bitfixer/petdisk-max/idf/main/EspHttp.h

#ifndef __esp_http_h__
#define __esp_http_h__

#include "EspConn.h"
#include <stdint.h>

namespace bitfixer
{

struct __attribute__ ((packed)) urlInfo {
    char host[64];
    char url[64];
    char params[64];
    char urlstring[256];
    char blockData[512];
    char fileName[64];
};

class EspHttp 
{
public:
    EspHttp()
    : _espConn(NULL)
    {}

    EspHttp(EspConn* espConn) 
    : _espConn(espConn)
    {}

    ~EspHttp() {}

    void initWithParams(EspConn* espConn);
    bool postBlock(char* host, int port, char* url, char* params, uint8_t* buffer, uint16_t* bufferSize, int numBytes);
    uint8_t* makeRequest(const char* host, int port, const char* url, const char* params, uint8_t* buffer, uint16_t* bufferSize, int* size);
    uint32_t getSize(const char* host, int port, const char* url, uint8_t* buffer, uint16_t* bufferSize);
    uint8_t* getRange(const char* host, int port, const char* url, uint32_t start, uint32_t end, uint8_t* buffer, uint16_t* bufferSize, int* size);

    int getSizeE(const char* host, const char* url, uint8_t* buffer, uint16_t* bufferSize);

private:
    EspConn* _espConn;

    uint8_t sendBuffer[2048];
};

}

#endif
