bitfixer/petdisk-max/idf/main/base64.cpp

/*
* Base64 encoding/decoding (RFC1341)
* Copyright (c) 2005-2011, Jouni Malinen <j@w1.fi>
*
* This software may be distributed under the terms of the BSD license.
* See README for more details.
*/
#include "base64.hpp"
#include <string.h>

static const unsigned char base64_table[65] =
    "ABCDEFGHIJKLMNOPQRSTUVWXYZabcdefghijklmnopqrstuvwxyz0123456789+/";

/**
* base64_encode - Base64 encode
* @src: Data to be encoded
* @len: Length of the data to be encoded
* @out_len: Pointer to output length variable, or %NULL if not used
* Returns: Allocated buffer of out_len bytes of encoded data,
* or empty string on failure
*/
int base64_len(int len) {
    return 4*((len + 2) / 3);
}

int base64_encode(const uint8_t* src, int len, uint8_t* out)
{
    unsigned char *pos;
    const unsigned char *end, *in;

    int olen = base64_len(len);

    end = src + len;
    in = src;
    pos = out;
    while (end - in >= 3) {
        *pos++ = base64_table[in[0] >> 2];
        *pos++ = base64_table[((in[0] & 0x03) << 4) | (in[1] >> 4)];
        *pos++ = base64_table[((in[1] & 0x0f) << 2) | (in[2] >> 6)];
        *pos++ = base64_table[in[2] & 0x3f];
        in += 3;
    }

    if (end - in) {
        *pos++ = base64_table[in[0] >> 2];
        if (end - in == 1) {
            *pos++ = base64_table[(in[0] & 0x03) << 4];
            *pos++ = '=';
        }
        else {
            *pos++ = base64_table[((in[0] & 0x03) << 4) |
                (in[1] >> 4)];
            *pos++ = base64_table[(in[1] & 0x0f) << 2];
        }
        *pos++ = '=';
    }

    return olen;
}
