bitfixer/petdisk-max/idf/main/cbmlayout.h

unsigned char LAYOUT_CBM[] = {
  0x00, 0x00, 0x00, 0x00, 0x00, 0x15, 0x00, 0x00, 0x00, 0x2a, 0x00, 0x00,
  0x00, 0x3f, 0x00, 0x00, 0x00, 0x54, 0x00, 0x00, 0x00, 0x69, 0x00, 0x00,
  0x00, 0x7e, 0x00, 0x00, 0x00, 0x93, 0x00, 0x00, 0x00, 0xa8, 0x00, 0x00,
  0x00, 0xbd, 0x00, 0x00, 0x00, 0xd2, 0x00, 0x00, 0x00, 0xe7, 0x00, 0x00,
  0x00, 0xfc, 0x00, 0x00, 0x00, 0x11, 0x01, 0x00, 0x00, 0x26, 0x01, 0x00,
  0x00, 0x3b, 0x01, 0x00, 0x00, 0x50, 0x01, 0x00, 0x00, 0x65, 0x01, 0x00,
  0x00, 0x78, 0x01, 0x00, 0x00, 0x8b, 0x01, 0x00, 0x00, 0x9e, 0x01, 0x00,
  0x00, 0xb1, 0x01, 0x00, 0x00, 0xc4, 0x01, 0x00, 0x00, 0xd7, 0x01, 0x00,
  0x00, 0xea, 0x01, 0x00, 0x00, 0xfc, 0x01, 0x00, 0x00, 0x0e, 0x02, 0x00,
  0x00, 0x20, 0x02, 0x00, 0x00, 0x32, 0x02, 0x00, 0x00, 0x44, 0x02, 0x00,
  0x00, 0x56, 0x02, 0x00, 0x00, 0x67, 0x02, 0x00, 0x00, 0x78, 0x02, 0x00,
  0x00, 0x89, 0x02, 0x00, 0x00, 0x9a, 0x02, 0x00, 0x00, 0xab, 0x02, 0x00,
  0x00, 0xbc, 0x02, 0x00, 0x00, 0xcd, 0x02, 0x00, 0x00, 0xde, 0x02, 0x00,
  0x00, 0xef, 0x02, 0x00, 0x00, 0x00, 0x03, 0x00
};
unsigned int LAYOUT_CBM_len = 164;
